ak66666/ThumbsUpV12_Omron/Photos/rev.3/IMG_20260313_220351697_HDR.jpg

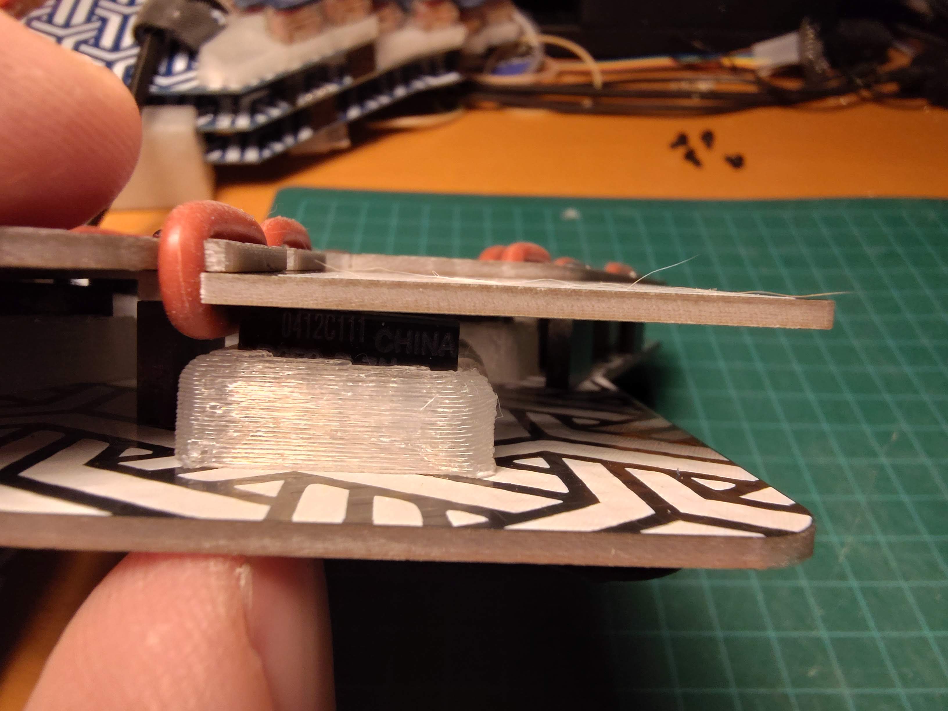
Photos/rev.3/IMG_20260313_220351697_HDR.jpg
