ak66666/ThumbsUpV12_Omron/Silkscreens/44 Key Keyboard Layout 20 pct.png

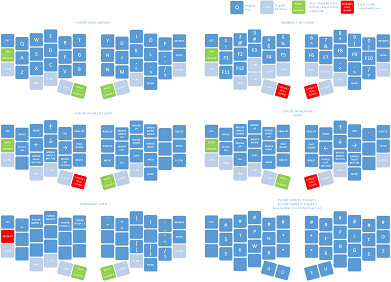
Silkscreens/44 Key Keyboard Layout 20 pct.png
