ak66666/ThumbsUpV12_Omron/Silkscreens/Pattern.png

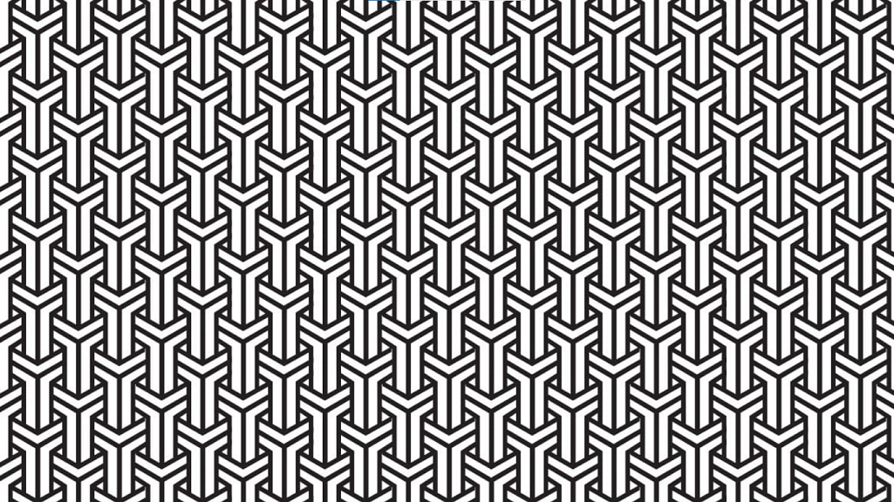
Silkscreens/Pattern.png
