ak66666/ThumbsUpV12_Omron/Silkscreens/QWERTY.png

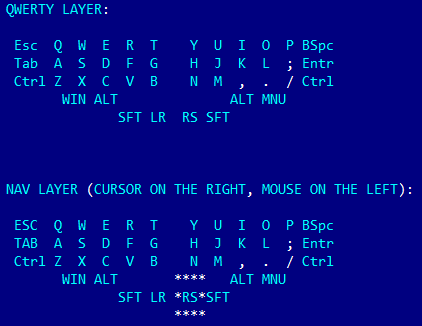
Silkscreens/QWERTY.png
